elipsitz/gameboy-fpga/sim/simulator.hpp

#pragma once

#include "cartridge.hpp"
#include "VSimGameboy.h"

struct JoypadState {
    bool start;
    bool select;
    bool b;
    bool a;
    bool down;
    bool up;
    bool left;
    bool right;
};

class Simulator {
public:
    Simulator(std::unique_ptr<Cartridge> cart);
    ~Simulator();

    void set_joypad_state(JoypadState state);
    void simulate_cycles(uint64_t cycles);
    void simulate_frame();
    void reset();
    std::vector<uint8_t>& getFramebuffer();
    std::vector<int16_t>& getAudioSampleBuffer();

private:
    void stepFramebuffer();
    void stepAudio();

    std::unique_ptr<Cartridge> cart;
    std::vector<uint8_t> framebuffer0;
    std::vector<uint8_t> framebuffer1;
    bool activeFramebuffer = false;
    uint64_t cycles = 0;
    VSimGameboy* top = nullptr;
    size_t framebufferIndex = 0;
    bool prev_vblank = false;
    bool prev_hblank = false;
    bool prev_lcd_enabled = false;
    std::vector<int16_t> audioSampleBuffer;
    int audioTimer = 0;
};
